johannesc/mspa-wifi/kicad/mspa-wifi/mspa-wifi.kicad_sch

## KiCad design kicad/mspa-wifi/mspa-wifi.kicad_sch (2025-05-04)

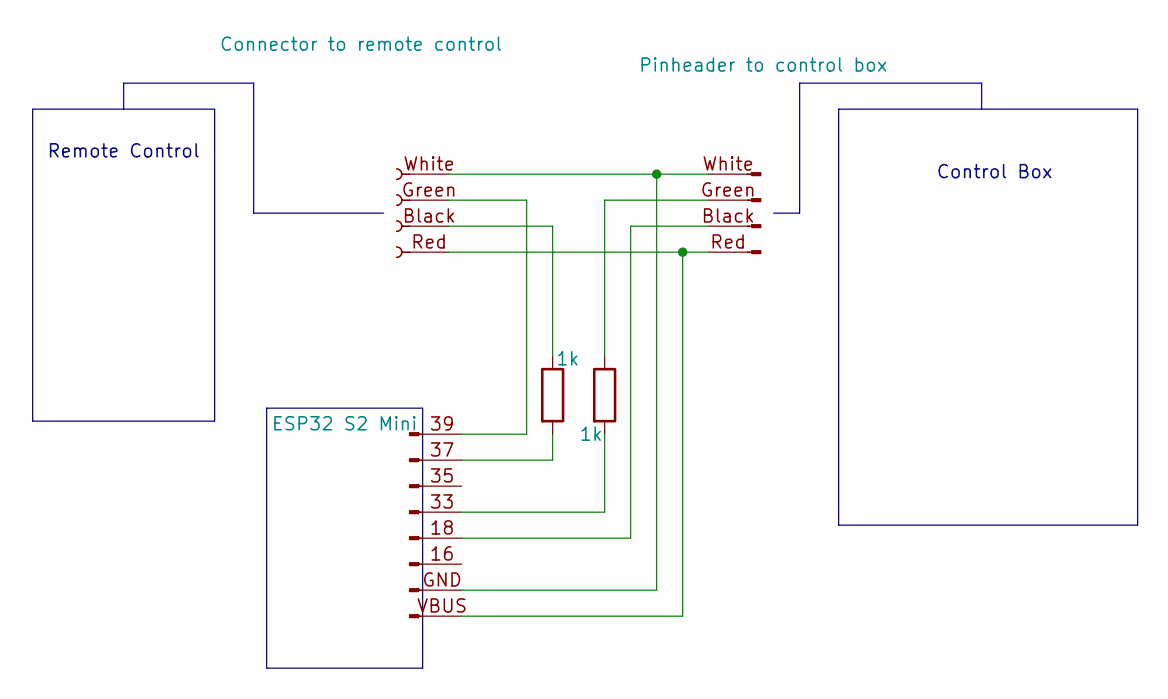
[picture p10: schematic mspa-wifi.kicad_sch]

Parts:
J1: Pinheader to control box
J2: Connector to remote control
J3: ESP32 S2 Mini
R1, R2: 1k

Connections:
unnamed: J1.Black (Pin_3), J3.18 (Pin_5)
unnamed: J1.Green (Pin_2), R2.1
unnamed: J1.Red (Pin_4), J2.Red (Pin_4), J3.VBUS (Pin_8)
unnamed: J1.White (Pin_1), J2.White (Pin_1), J3.GND (Pin_7)
unnamed: J2.Black (Pin_3), R1.1
unnamed: J2.Green (Pin_2), J3.39 (Pin_1)
unnamed: J3.33 (Pin_4), R2.2
unnamed: J3.37 (Pin_2), R1.2

Notes on the sheet:
Remote Control
Control Box
