johannesc/mspa-wifi/esphome/components/mspa_wifi/mspa_number.cpp

#include "esphome/core/component.h"
#include "esphome/core/log.h"
#include "mspa_number.h"

namespace esphome
{
    namespace mspa_wifi
    {
        static const char *TAG = "mspa.number";

        void MspaNumber::setup()
        {
        }

        void MspaNumber::control(float value)
        {
            if (mspa_ == nullptr)
            {
                ESP_LOGI(TAG, "mspa_ was not set");
                return;
            }
            if (value == last_value_)
            {
                return;
            }
            last_value_ = value;

            switch (type_)
            {
            case MspaNumberType::TARGET_TEMP:
                ESP_LOGI(TAG, "New target temp from HA: %f", value);
                mspa_->set_target_water_temperature(value);
                break;

            case MspaNumberType::BUBBLE_SPEED:
                ESP_LOGI(TAG, "New bubble speed from HA: %f", value);
                mspa_->set_bubble_speed(value);
                break;
            }

            this->publish_state(value);
        }

        void MspaNumber::dump_config()
        {
            ESP_LOGCONFIG(TAG, "MspaNumber: %d", type_);
        }

    } // namespace mspa_wifi
} // namespace esphome
